timonsku/Cool-S-Badge/docs/upload_auterm.png

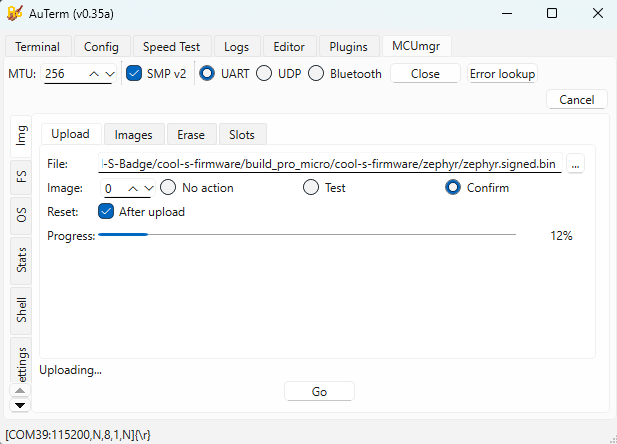
docs/upload_auterm.png
