timonsku/Cool-S-Badge/docs/assembly/3.jpg

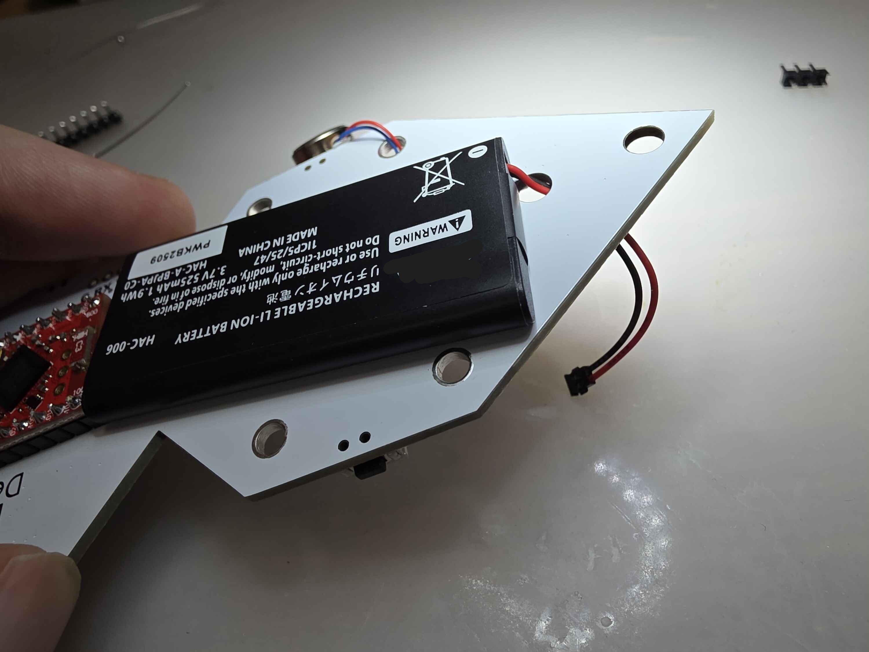
docs/assembly/3.jpg
